dariuskl/mspmeter/src/adc.hpp

// Meter Firmware / Darius Kellermann <kellermann@proton.me>

#ifndef MSPMETER_ADC_HPP
#define MSPMETER_ADC_HPP

#include "config.hpp"
#include "msp430i2.hpp"

namespace meter {

  class AD_converter {
    public:
      static void init() {
        using namespace msp430i2;

        store(SD24CTL, SD24REFS);
        store(SD24CCTL0, SD24LSBTOG | SD24DF | SD24IE | SD24GRP);
        store(SD24CCTL1, SD24LSBTOG | SD24DF | SD24GRP);
        store(SD24CCTL2, SD24LSBTOG | SD24DF | SD24GRP);
        store(SD24CCTL3, SD24LSBTOG | SD24DF);
      }

      static void start_conversion() { msp430i2::SD24::start_conversion<3>(); }
      static void stop_conversion() { msp430i2::SD24::stop_conversion<3>(); }

      static bool overflow() { return msp430i2::SD24::any_overflow(); }

      constexpr int32_t get_conversion_result(const int channel) {
        return averages_[channel];
      }

      static constexpr int32_t to_uV(const int32_t conversion_result) {
        return static_cast<int32_t>(
            (int64_t{conversion_result} * msp430i2::SD24::reference_uV)
            / msp430i2::SD24::full_scale);
      }

      /// \return Whether a new averaged result is available.
      bool on_conversion_done() {
        for (auto i = 0; i < used_channels; ++i) {
          sums_[i] += msp430i2::SD24::get_conversion_result(i);
        }
        ++number_of_conversion_results_;

        if (number_of_conversion_results_ >= number_of_oversamples) {
          stop_conversion();
          for (auto i = 0; i < used_channels; ++i) {
            averages_[i] = sums_[i] / number_of_conversion_results_;
          }
          sums_ = {};
          number_of_conversion_results_ = 0;
          return true;
        }
        return false;
      }

    private:
      Array<int32_t, used_channels> sums_{};
      Array<int32_t, used_channels> averages_{};
      Size number_of_conversion_results_{};
  };

} // namespace meter

#endif // MSPMETER_ADC_HPP
